AntoBrandi/Dextro-Bot/CAD/Electronics/Raspberry PI 3.SLDPRT

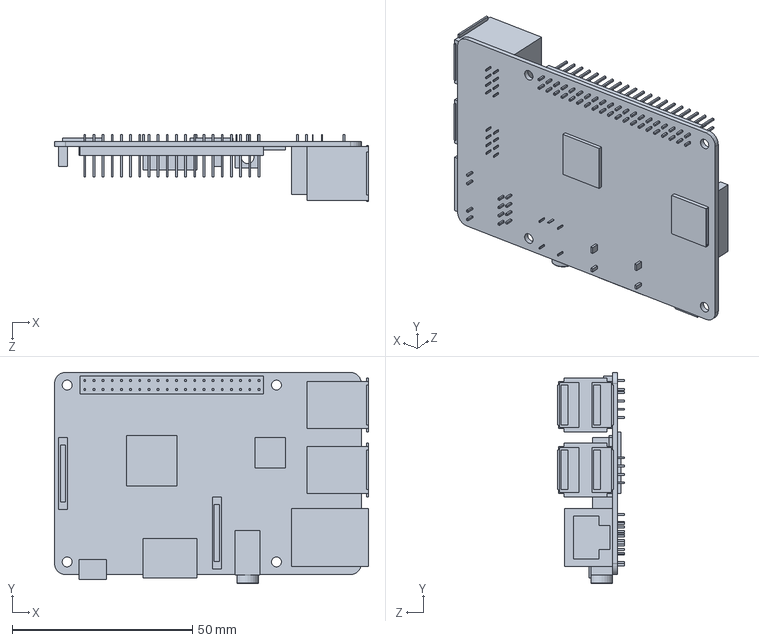
[picture p25: CAD file, 2020-10-17]
CAD/Electronics/Raspberry PI 3.SLDPRT
87.0 x 58.5 x 18.6 mm
