AntoBrandi/Dextro-Bot/CAD/pi support 1.SLDPRT

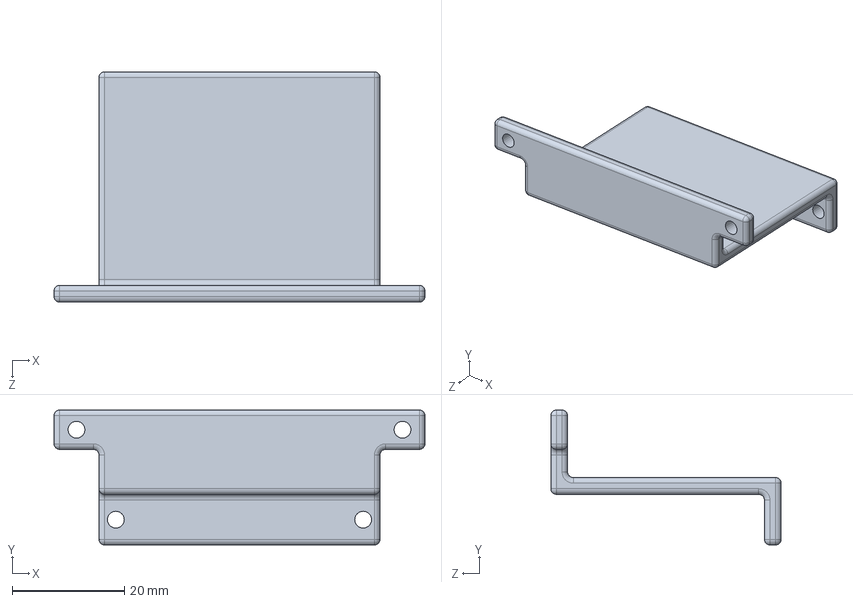
[picture p26: CAD file, 2020-08-17]
CAD/pi support 1.SLDPRT
66.0 x 24.0 x 41.0 mm
