AntoBrandi/Dextro-Bot/CAD/rev_2/carena_right.SLDPRT

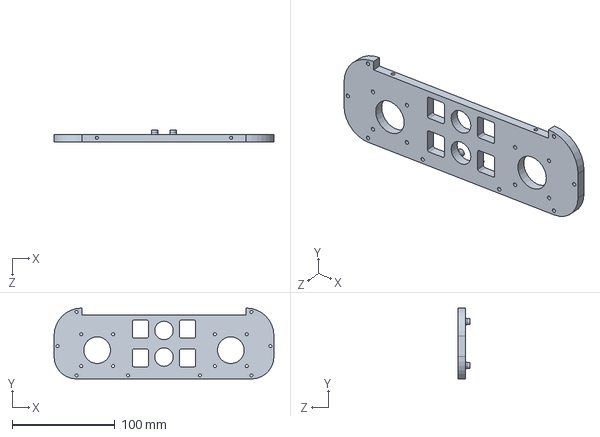
[picture p27: CAD file, 2020-10-18]
CAD/rev_2/carena_right.SLDPRT
214.0 x 69.0 x 11.5 mm
