AntoBrandi/Dextro-Bot/CAD/Servo/bottom.SLDPRT

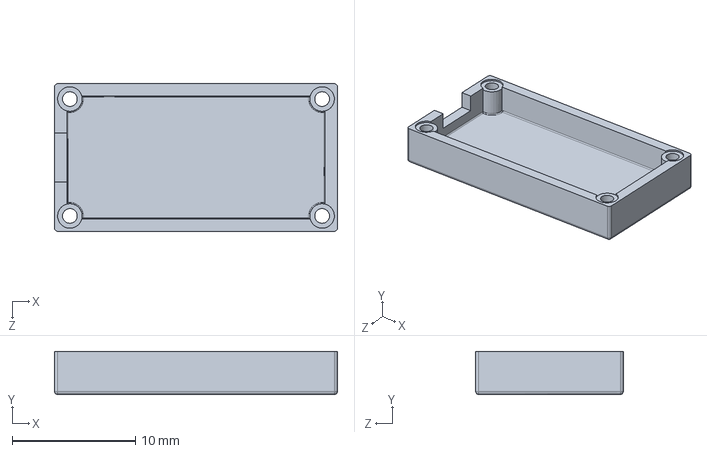
[picture p28: CAD file, 2020-07-25]
CAD/Servo/bottom.SLDPRT
23.0 x 3.50 x 12.0 mm
