AntoBrandi/Dextro-Bot/ROS/dextrobot_ws/src/robotnik_sensors/meshes/sick_microscan3.stl

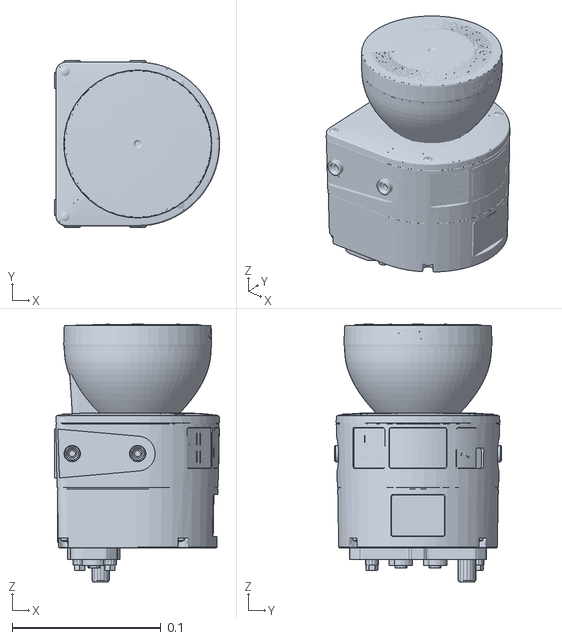
[picture p29: CAD file, 2020-08-21]
ROS/dextrobot_ws/src/robotnik_sensors/meshes/sick_microscan3.stl
0.111 x 0.112 x 0.174
