AntoBrandi/Dextro-Bot/STL/carena_top_rev.STL

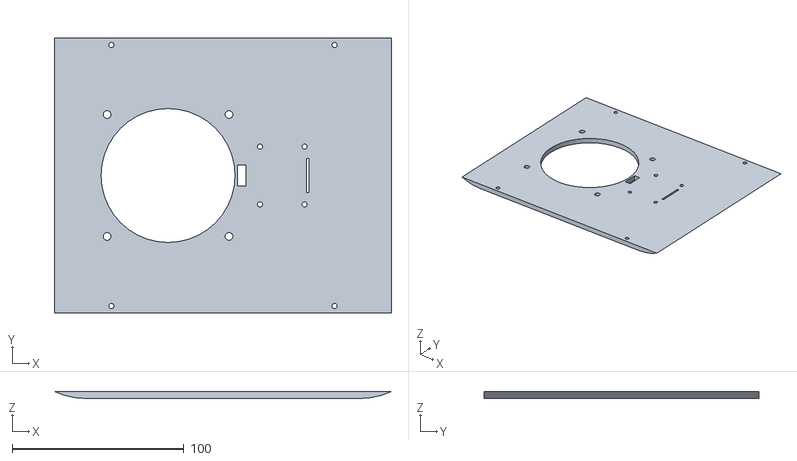
[picture p30: CAD file, 2020-07-25]
STL/carena_top_rev.STL
196.3 x 160.0 x 4.00
