AntoBrandi/Dextro-Bot/CAD/Electronics/Arduino Uno CNC Shield V3.SLDPRT

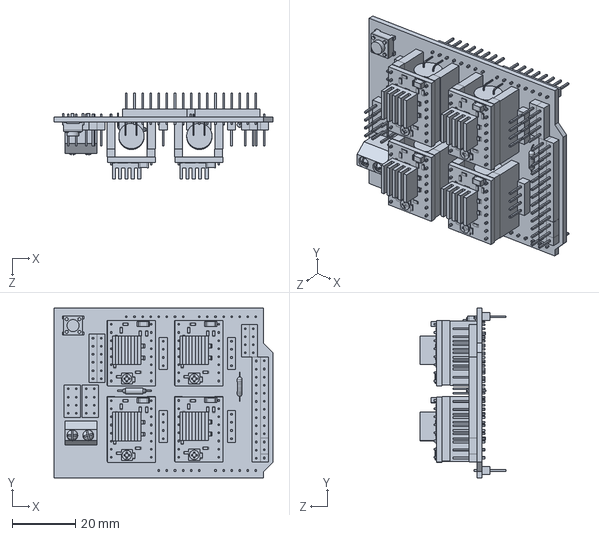
[picture p31: CAD file, 2020-10-17]
CAD/Electronics/Arduino Uno CNC Shield V3.SLDPRT
69.0 x 53.5 x 27.1 mm
