AntoBrandi/Dextro-Bot/CAD/pi support 2.SLDPRT

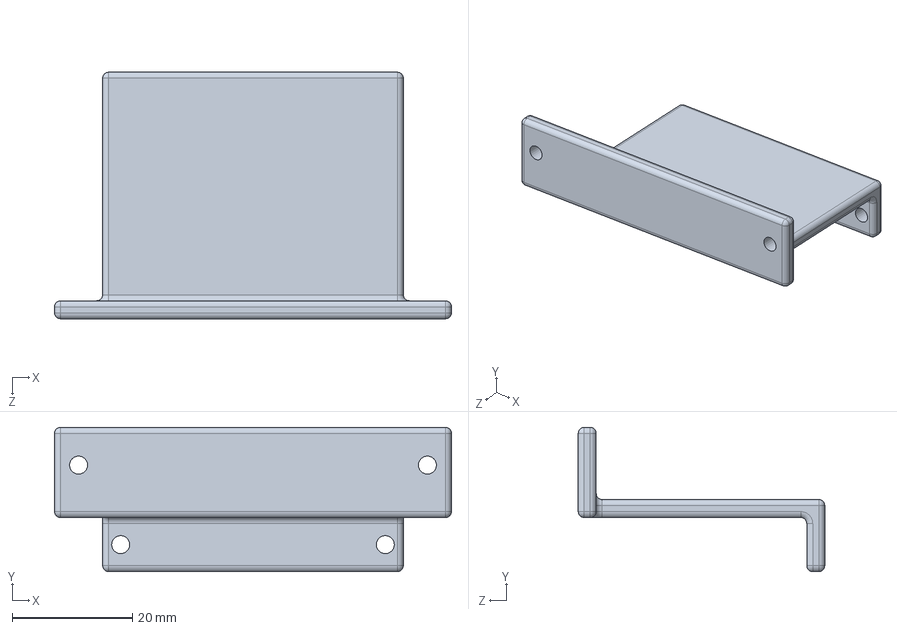
[picture p32: CAD file, 2020-08-17]
CAD/pi support 2.SLDPRT
66.0 x 24.0 x 41.0 mm
