AntoBrandi/Dextro-Bot/CAD/Servo/middle.SLDPRT

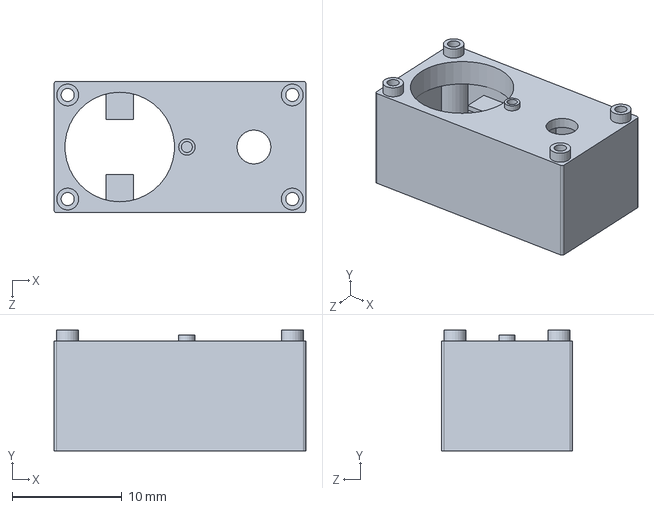
[picture p33: CAD file, 2020-07-25]
CAD/Servo/middle.SLDPRT
23.0 x 11.0 x 12.0 mm
