AntoBrandi/Dextro-Bot/ROS/dextrobot_ws/src/robotnik_sensors/meshes/antenna_3GO16.stl

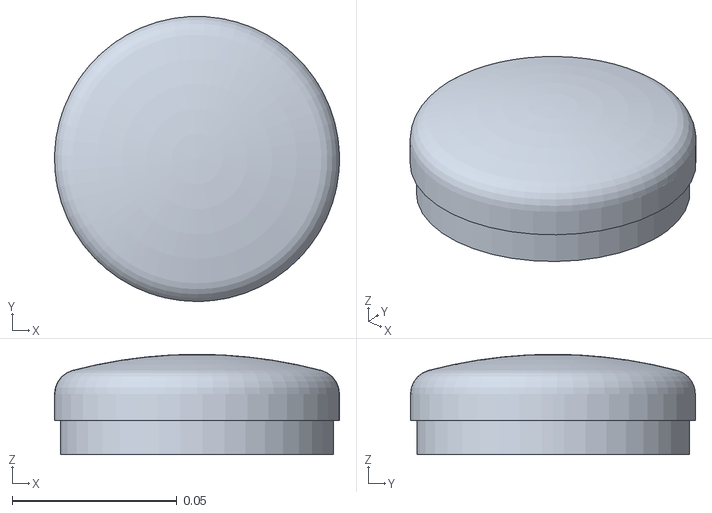
[picture p34: CAD file, 2020-08-21]
ROS/dextrobot_ws/src/robotnik_sensors/meshes/antenna_3GO16.stl
0.0866 x 0.0866 x 0.0305
