AntoBrandi/Dextro-Bot/STL/Base platform.STL

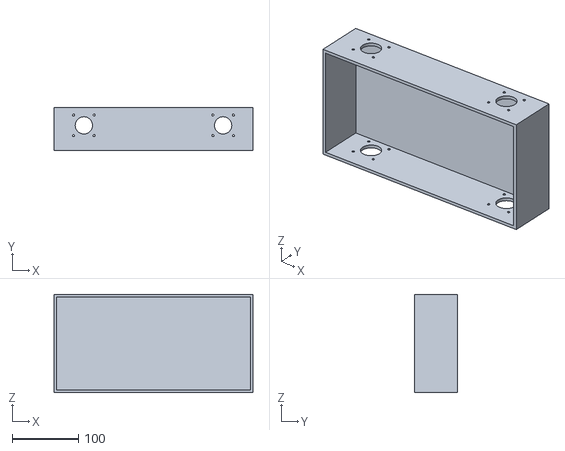
[picture p35: CAD file, 2020-07-25]
STL/Base platform.STL
300.0 x 65.0 x 148.0
