AntoBrandi/Dextro-Bot/CAD/Camera Stand v2.SLDPRT

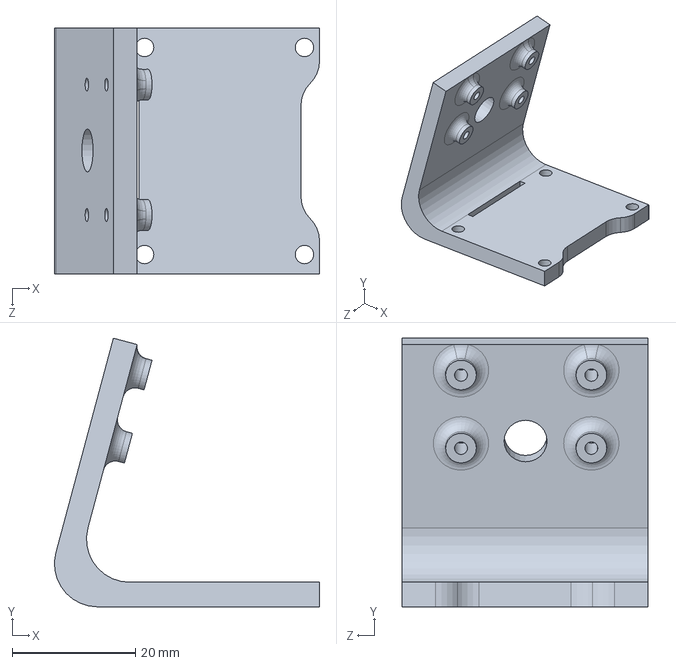
[picture p36: CAD file, 2020-08-13]
CAD/Camera Stand v2.SLDPRT
43.1 x 43.7 x 40.0 mm
