AntoBrandi/Dextro-Bot/CAD/Electronics/MPU_6050.SLDPRT

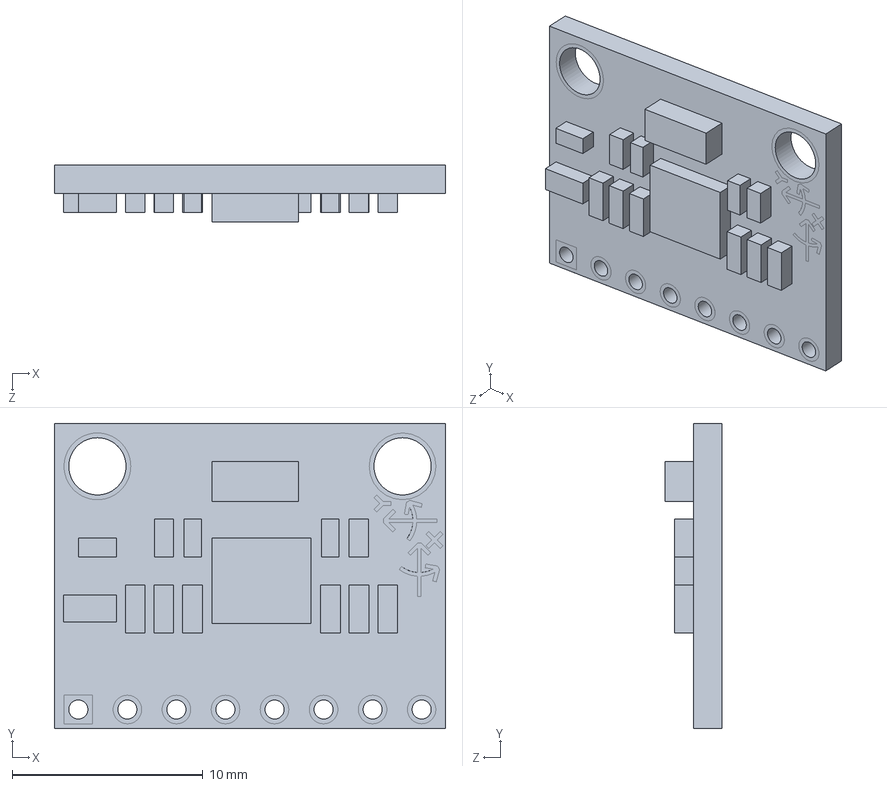
[picture p37: CAD file, 2020-10-17]
CAD/Electronics/MPU_6050.SLDPRT
20.5 x 16.0 x 3.00 mm
