AntoBrandi/Dextro-Bot/CAD/rev_2/carena_top.SLDPRT

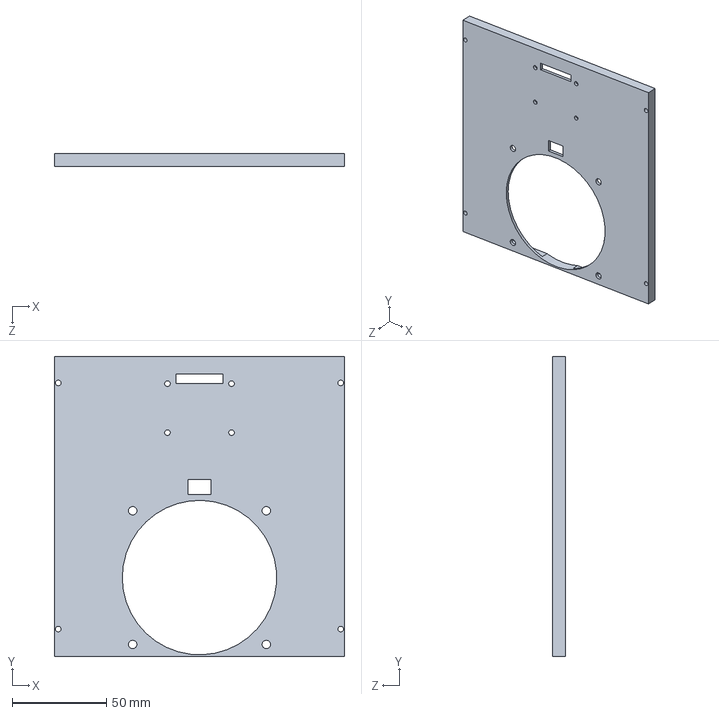
[picture p38: CAD file, 2020-10-18]
CAD/rev_2/carena_top.SLDPRT
154.0 x 159.5 x 7.00 mm
