AntoBrandi/Dextro-Bot/CAD/Servo/gear.SLDPRT

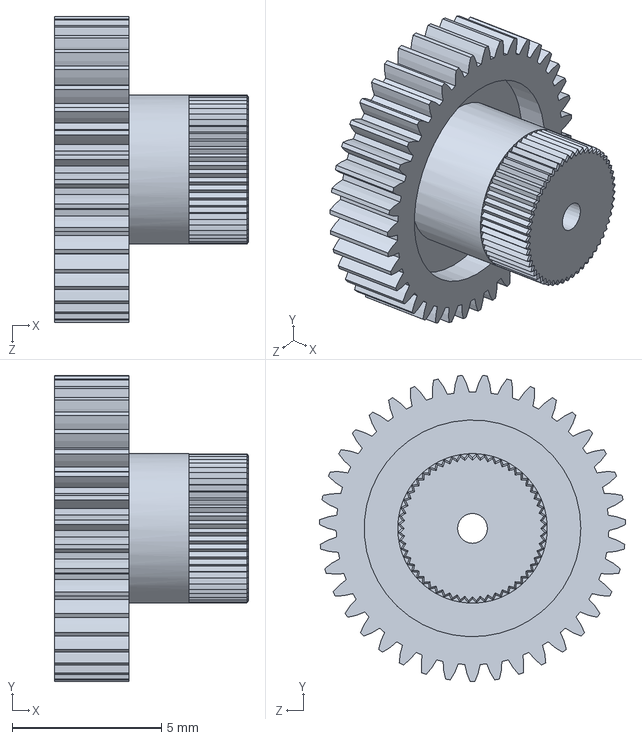
[picture p39: CAD file, 2020-07-25]
CAD/Servo/gear.SLDPRT
6.50 x 10.2 x 10.2 mm
