AntoBrandi/Dextro-Bot/ROS/dextrobot_ws/src/robotnik_sensors/meshes/hokuyo_utm_30lx.stl

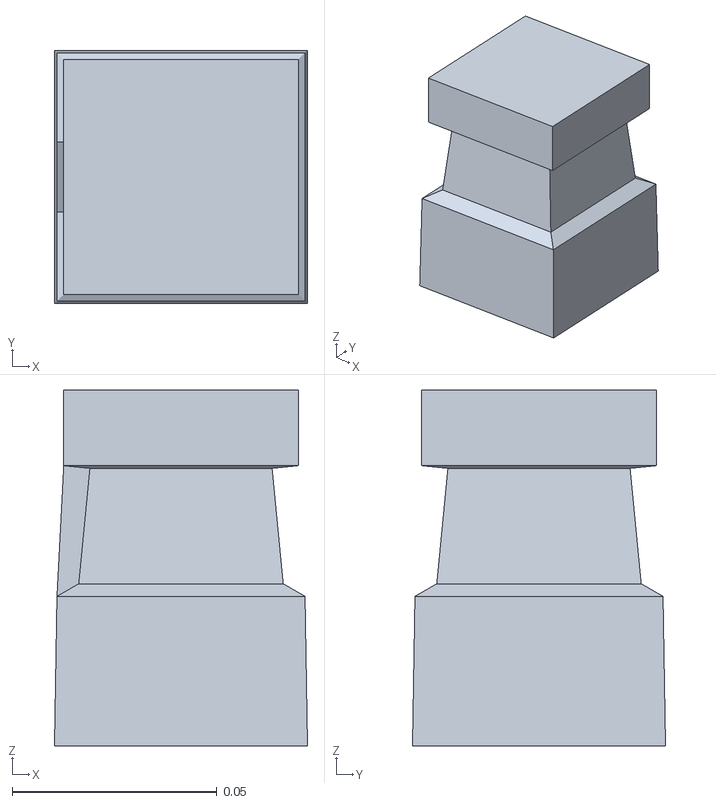
[picture p40: CAD file, 2020-08-21]
ROS/dextrobot_ws/src/robotnik_sensors/meshes/hokuyo_utm_30lx.stl
0.0618 x 0.0618 x 0.087
