AntoBrandi/Dextro-Bot/CAD/Electronics/RPi cam Rev 1.3.SLDPRT

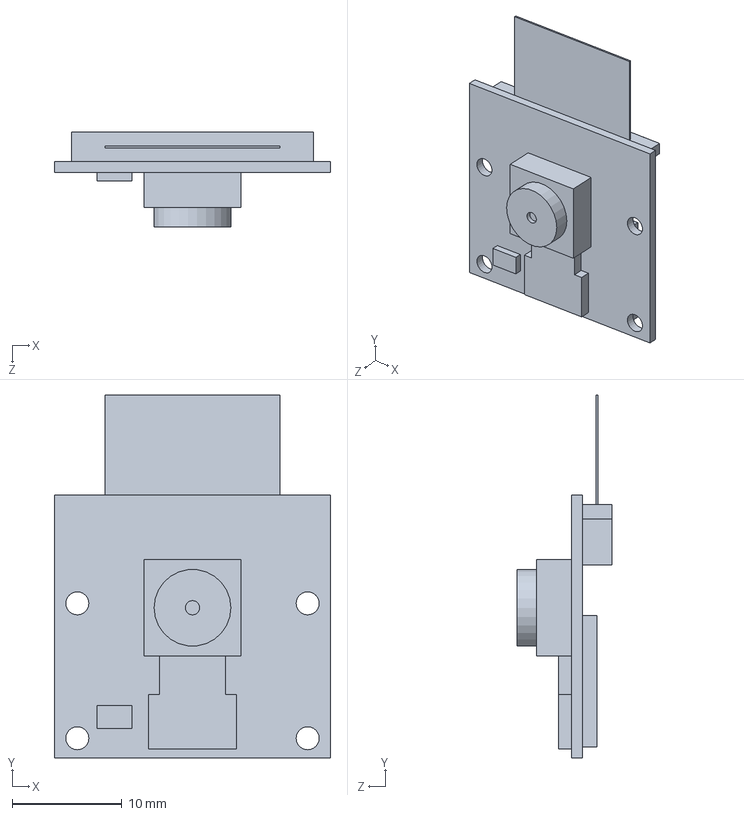
[picture p41: CAD file, 2020-07-25]
CAD/Electronics/RPi cam Rev 1.3.SLDPRT
25.2 x 33.1 x 8.70 mm
