AntoBrandi/Dextro-Bot/CAD/rev_2/battery_cover_2.SLDPRT

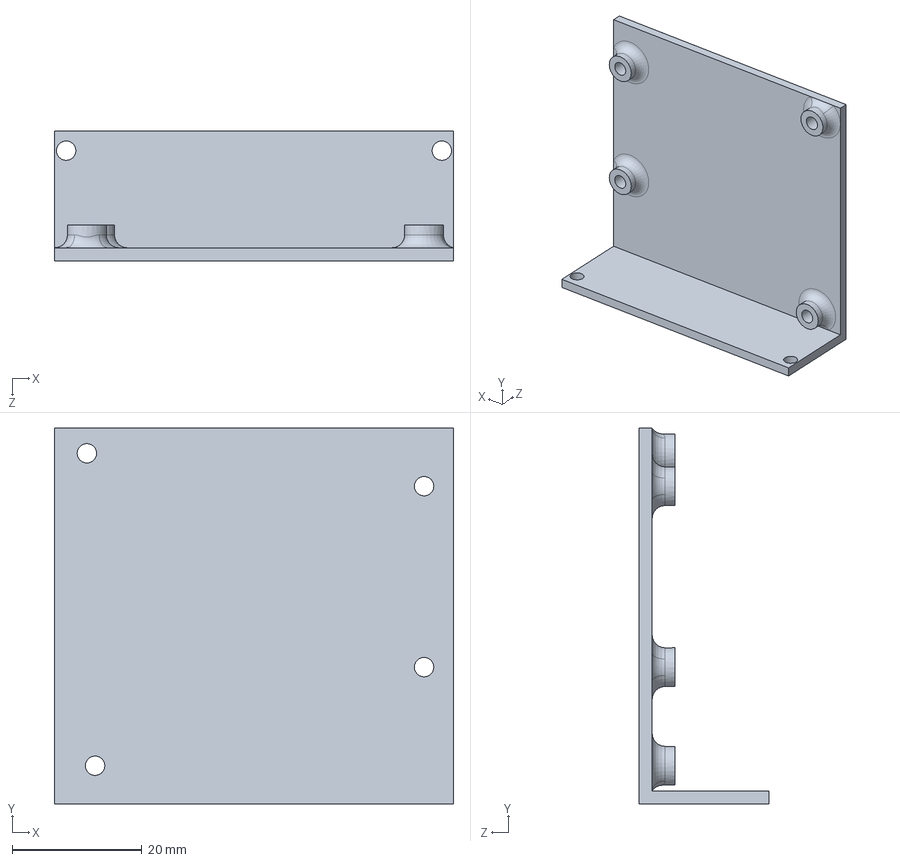
[picture p42: CAD file, 2020-10-18]
CAD/rev_2/battery_cover_2.SLDPRT
61.6 x 58.0 x 20.0 mm
