AntoBrandi/Dextro-Bot/ROS/dextrobot_ws/src/robotnik_sensors/meshes/intel_r430.stl

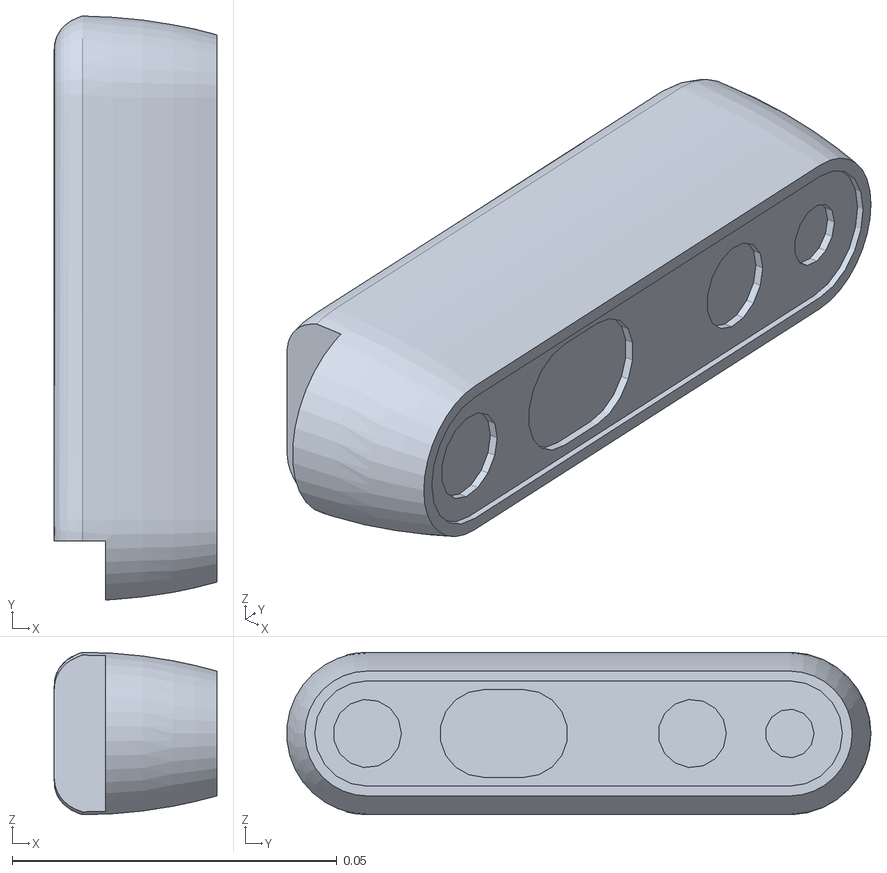
[picture p43: CAD file, 2020-08-21]
ROS/dextrobot_ws/src/robotnik_sensors/meshes/intel_r430.stl
0.025 x 0.0899 x 0.025
