AntoBrandi/Dextro-Bot/CAD/Electronics/FemaleUSB.SLDPRT

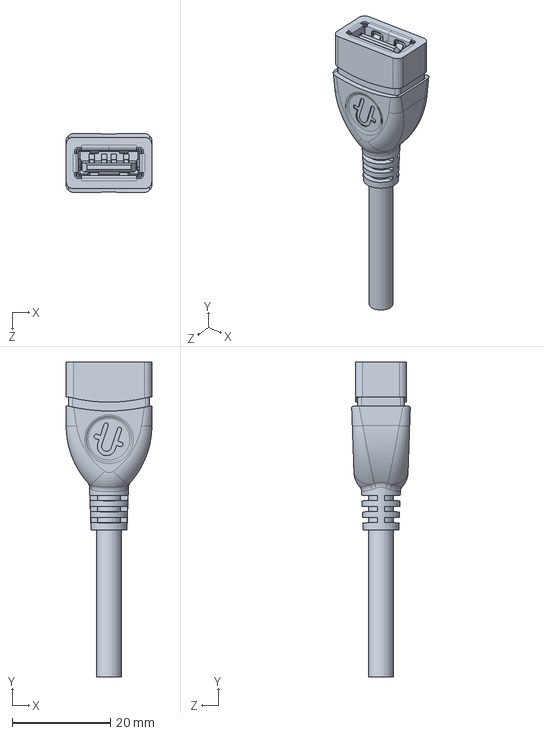
[picture p44: CAD file, 2020-07-25]
CAD/Electronics/FemaleUSB.SLDPRT
17.5 x 64.2 x 12.0 mm
