AntoBrandi/Dextro-Bot/CAD/Servo/top.SLDPRT

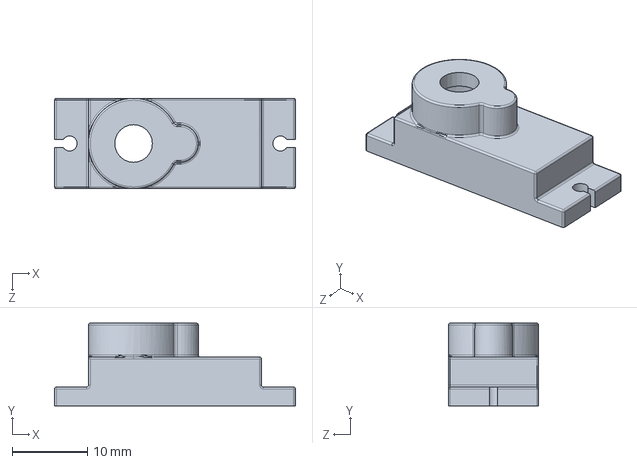
[picture p45: CAD file, 2020-07-25]
CAD/Servo/top.SLDPRT
32.0 x 11.0 x 12.0 mm
