AntoBrandi/Dextro-Bot/CAD/Electronics/XT60_Conector.SLDPRT

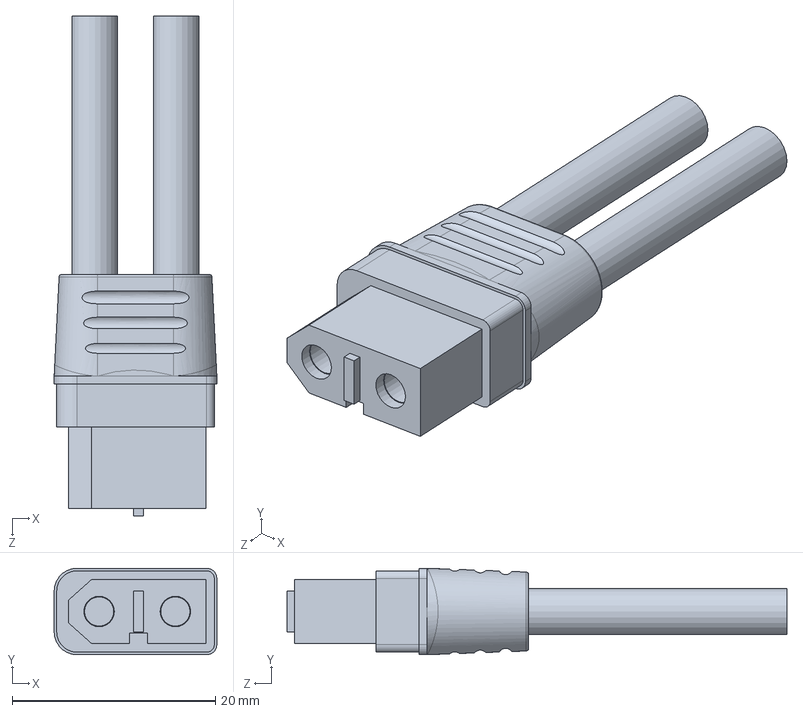
[picture p46: CAD file, 2020-07-25]
CAD/Electronics/XT60_Conector.SLDPRT
16.0 x 8.50 x 49.2 mm
