AntoBrandi/Dextro-Bot/CAD/rev_2/battery_cover_3.SLDPRT

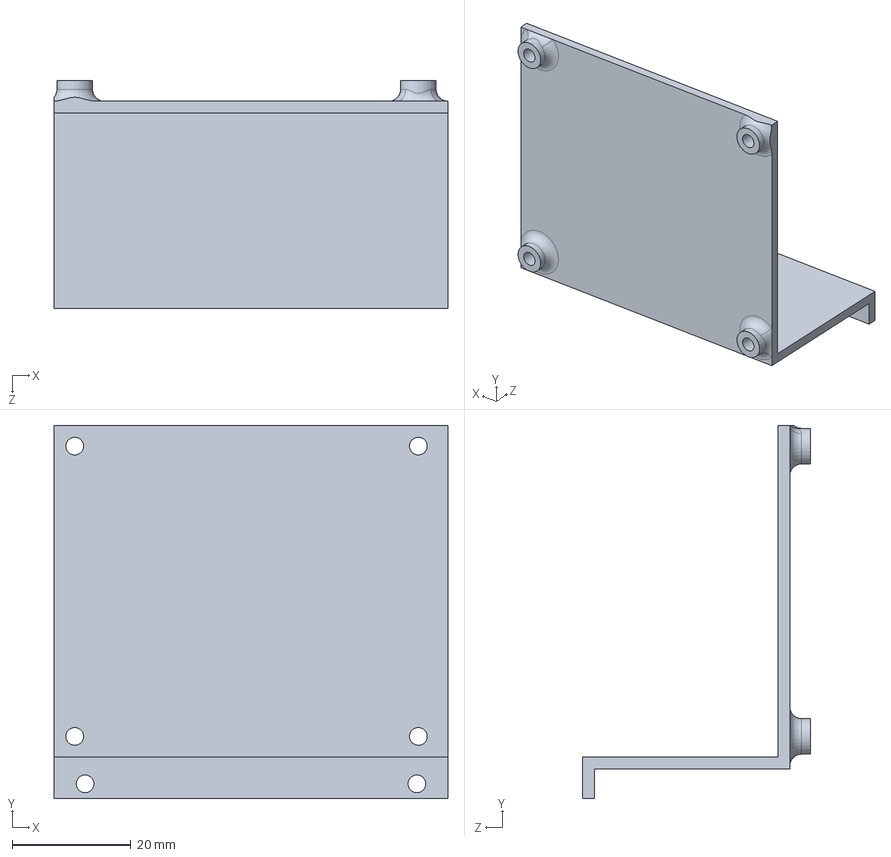
[picture p47: CAD file, 2020-10-18]
CAD/rev_2/battery_cover_3.SLDPRT
66.5 x 63.0 x 38.5 mm
