AntoBrandi/Dextro-Bot/ROS/dextrobot_ws/src/robotnik_sensors/meshes/axis_m5013.stl

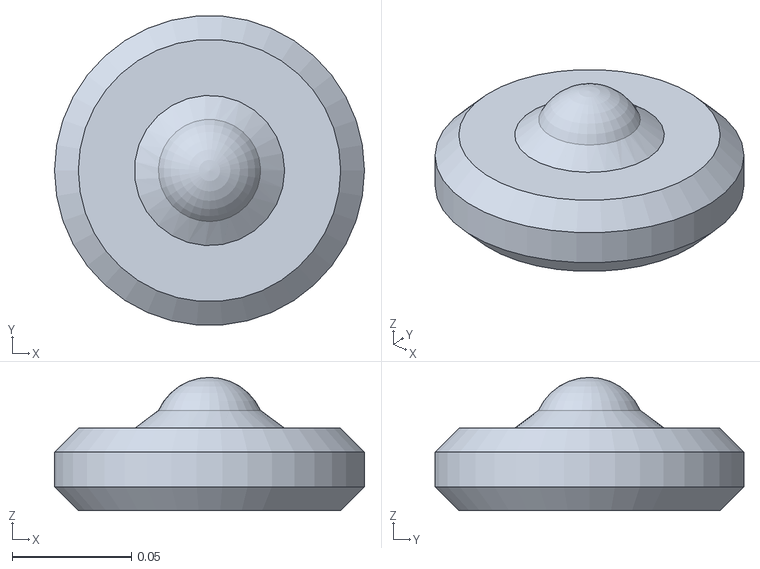
[picture p48: CAD file, 2020-08-21]
ROS/dextrobot_ws/src/robotnik_sensors/meshes/axis_m5013.stl
0.13 x 0.13 x 0.0559
