AntoBrandi/Dextro-Bot/CAD/Electronics/Nokia 6.1 plus.SLDPRT

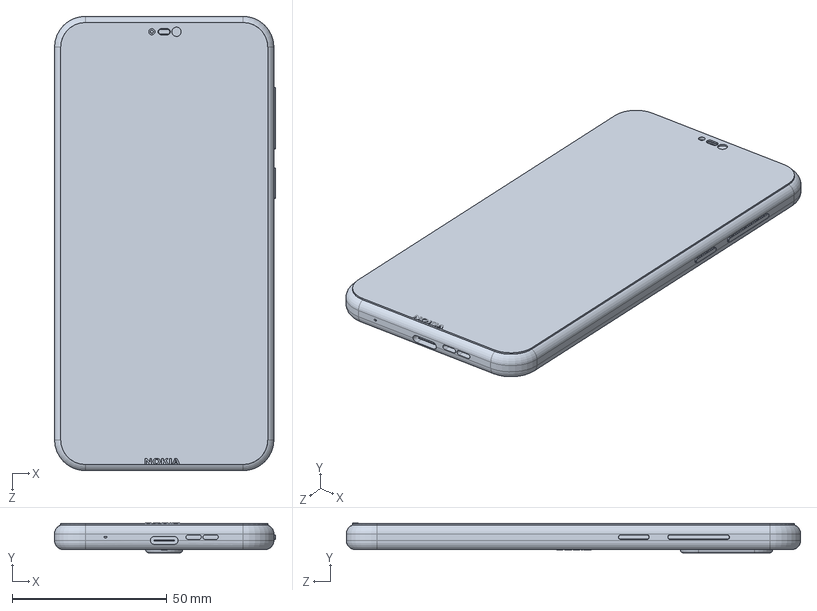
[picture p49: CAD file, 2020-07-25]
CAD/Electronics/Nokia 6.1 plus.SLDPRT
71.5 x 9.60 x 147.0 mm
