AntoBrandi/Dextro-Bot/CAD/rev_2/battery_cover.SLDPRT

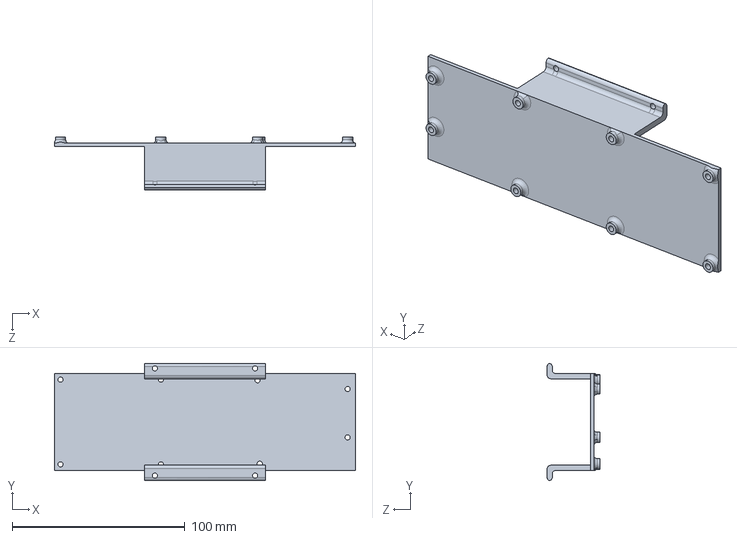
[picture p50: CAD file, 2020-10-17]
CAD/rev_2/battery_cover.SLDPRT
174.0 x 67.9 x 30.5 mm
