AntoBrandi/Dextro-Bot/ROS/dextrobot_ws/src/robotnik_sensors/meshes/ueye_cp_gige.stl

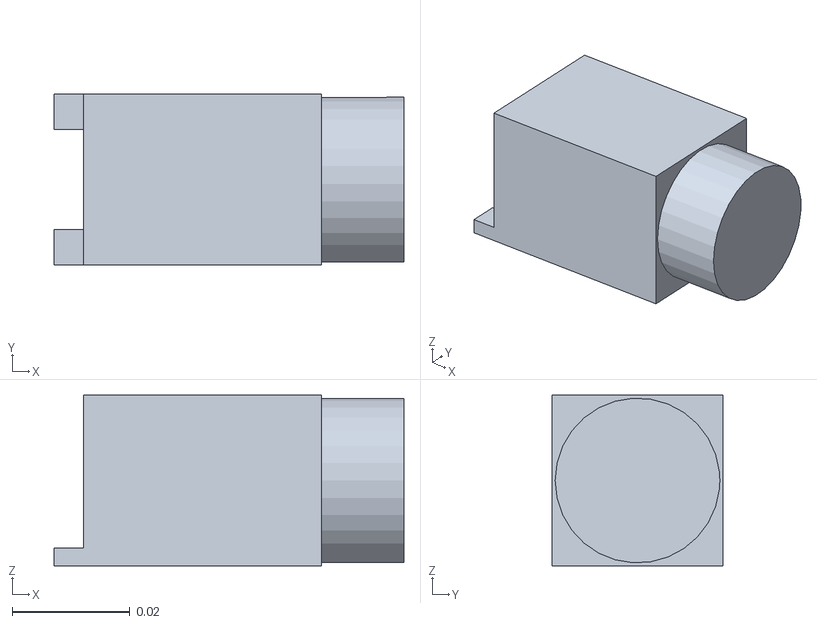
[picture p51: CAD file, 2020-08-21]
ROS/dextrobot_ws/src/robotnik_sensors/meshes/ueye_cp_gige.stl
0.0595 x 0.029 x 0.029
