AntoBrandi/Dextro-Bot/CAD/Electronics/Nema17.SLDPRT

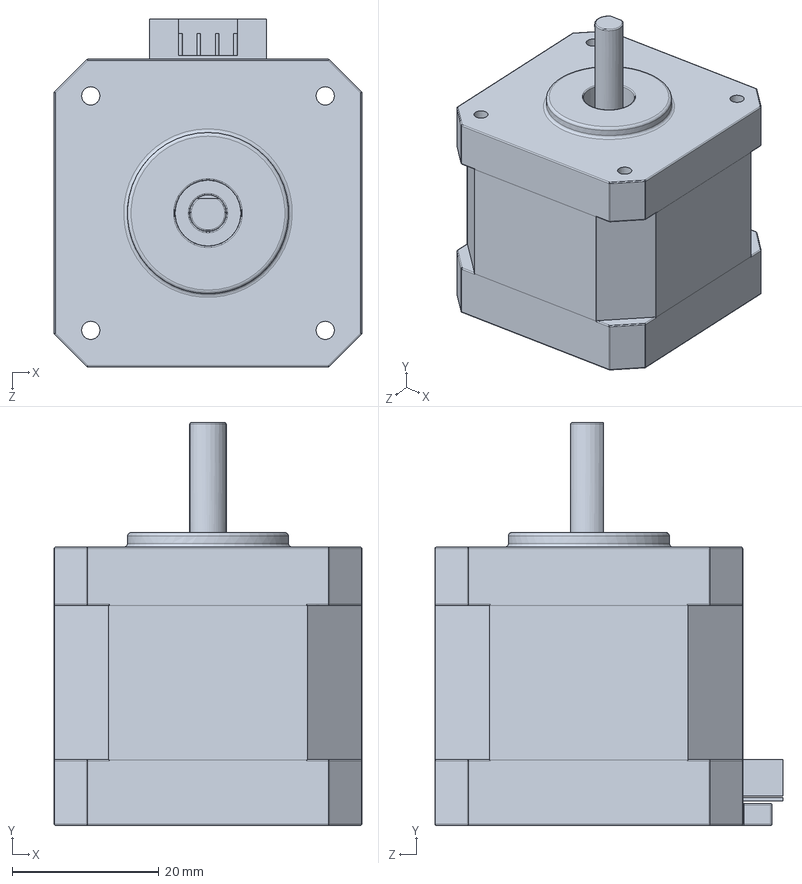
[picture p52: CAD file, 2020-07-25]
CAD/Electronics/Nema17.SLDPRT
42.0 x 55.0 x 47.5 mm
