AntoBrandi/Dextro-Bot/ROS/dextrobot_ws/src/robotnik_sensors/meshes/benewake_ce30.stl

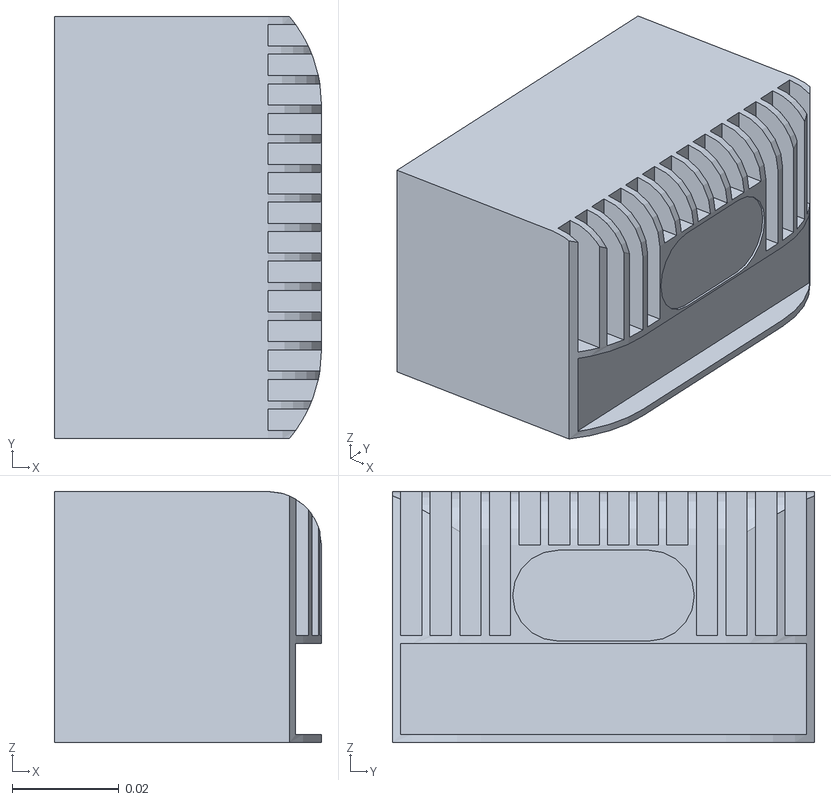
[picture p53: CAD file, 2020-08-21]
ROS/dextrobot_ws/src/robotnik_sensors/meshes/benewake_ce30.stl
0.05 x 0.079 x 0.047
