AntoBrandi/Dextro-Bot/CAD/Electronics/DRV 8825 .SLDPRT

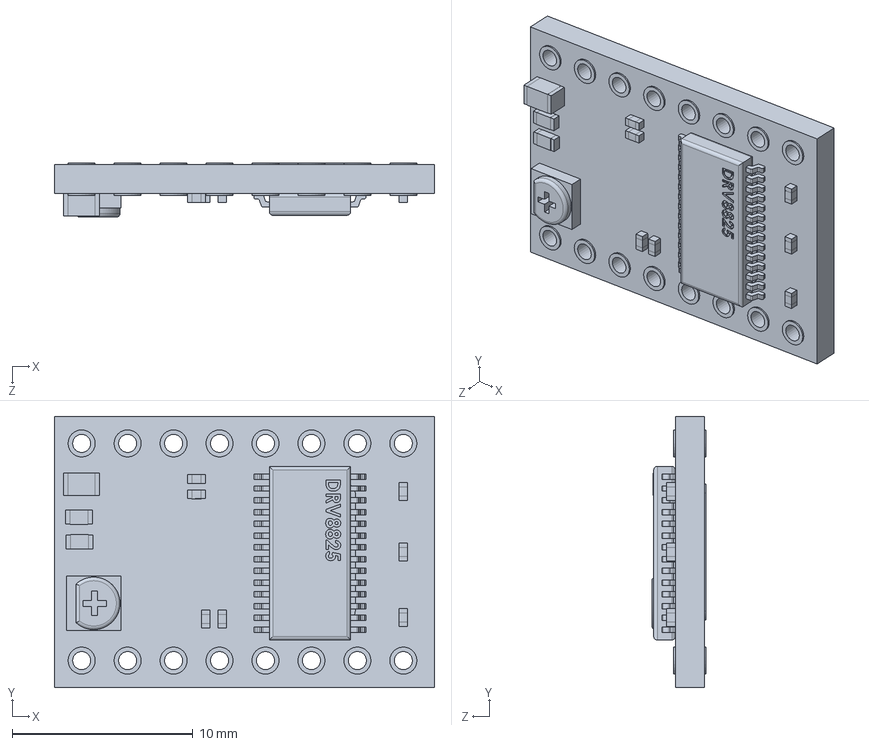
[picture p54: CAD file, 2020-07-25]
CAD/Electronics/DRV 8825 .SLDPRT
21.0 x 15.0 x 3.00 mm
