AntoBrandi/Dextro-Bot/ROS/dextrobot_ws/src/robotnik_sensors/meshes/kinectv2_nobase.stl

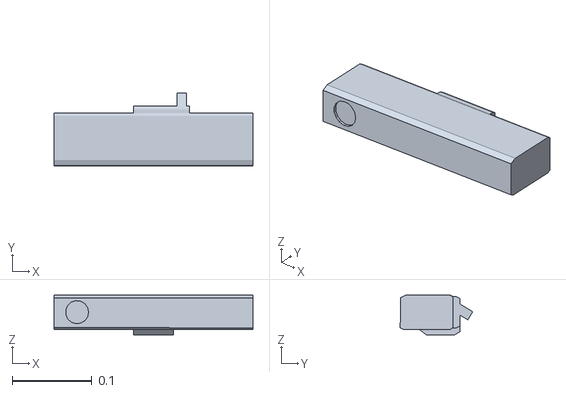
[picture p55: CAD file, 2020-08-21]
ROS/dextrobot_ws/src/robotnik_sensors/meshes/kinectv2_nobase.stl
0.25 x 0.0911 x 0.0501
