AntoBrandi/Dextro-Bot/CAD/Electronics/Female HDMI connector.SLDPRT

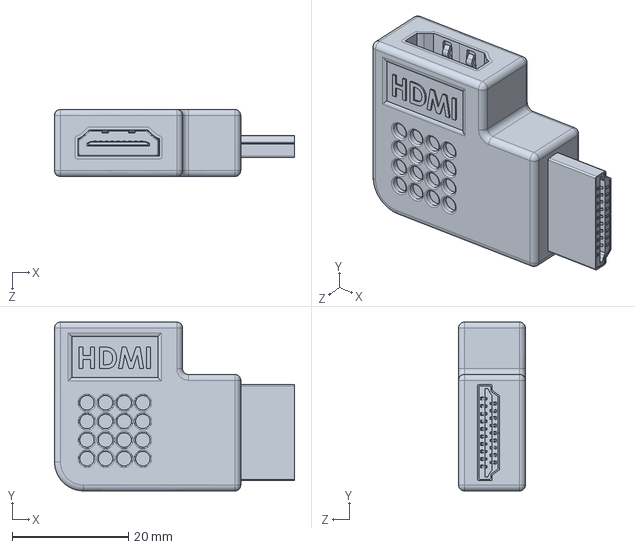
[picture p56: CAD file, 2020-07-25]
CAD/Electronics/Female HDMI connector.SLDPRT
41.2 x 29.0 x 11.5 mm
