AntoBrandi/Dextro-Bot/ROS/dextrobot_ws/src/robotnik_sensors/meshes/rslidar.stl

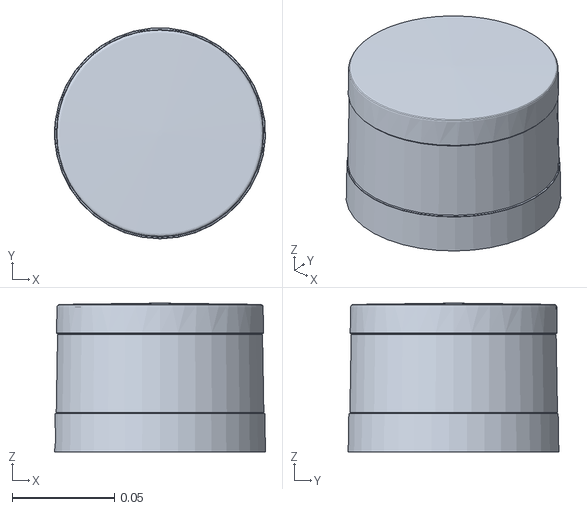
[picture p57: CAD file, 2020-08-21]
ROS/dextrobot_ws/src/robotnik_sensors/meshes/rslidar.stl
0.103 x 0.103 x 0.0727
