AntoBrandi/Dextro-Bot/CAD/Electronics/5 cell LiPo battery v7.SLDPRT

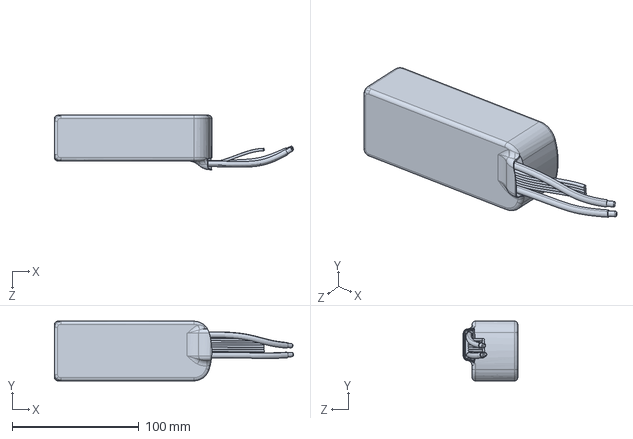
[picture p58: CAD file, 2020-07-25]
CAD/Electronics/5 cell LiPo battery v7.SLDPRT
188.3 x 47.0 x 43.0 mm
