AntoBrandi/Dextro-Bot/ROS/dextrobot_ws/src/robotnik_sensors/meshes/zed.stl

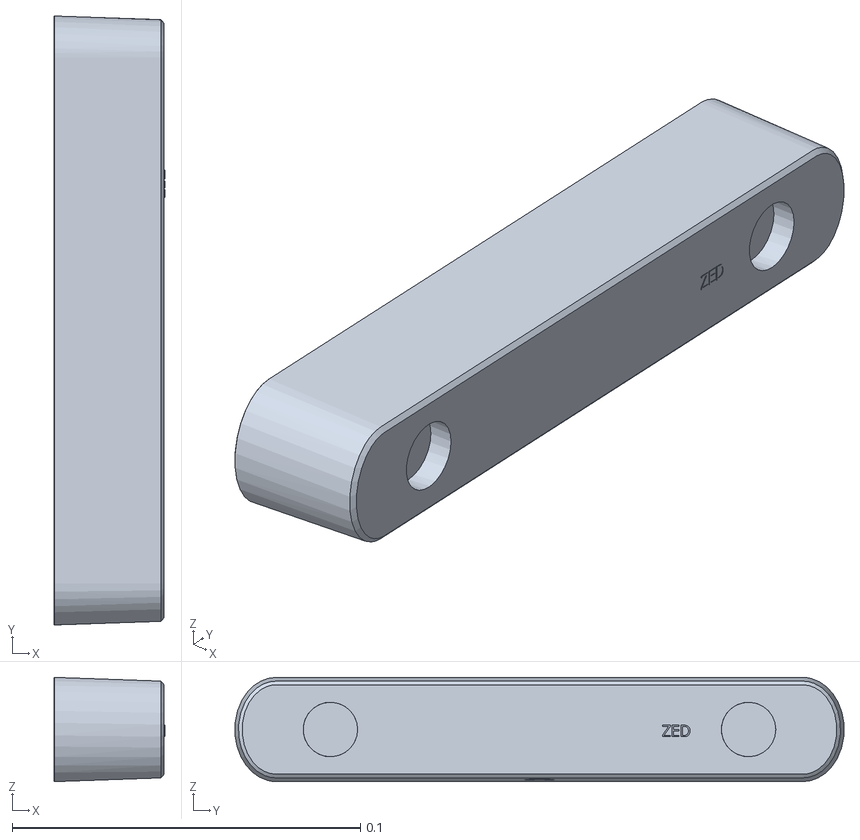
[picture p59: CAD file, 2020-08-21]
ROS/dextrobot_ws/src/robotnik_sensors/meshes/zed.stl
0.0318 x 0.175 x 0.0299
