AntoBrandi/Dextro-Bot/CAD/Roller.SLDPRT

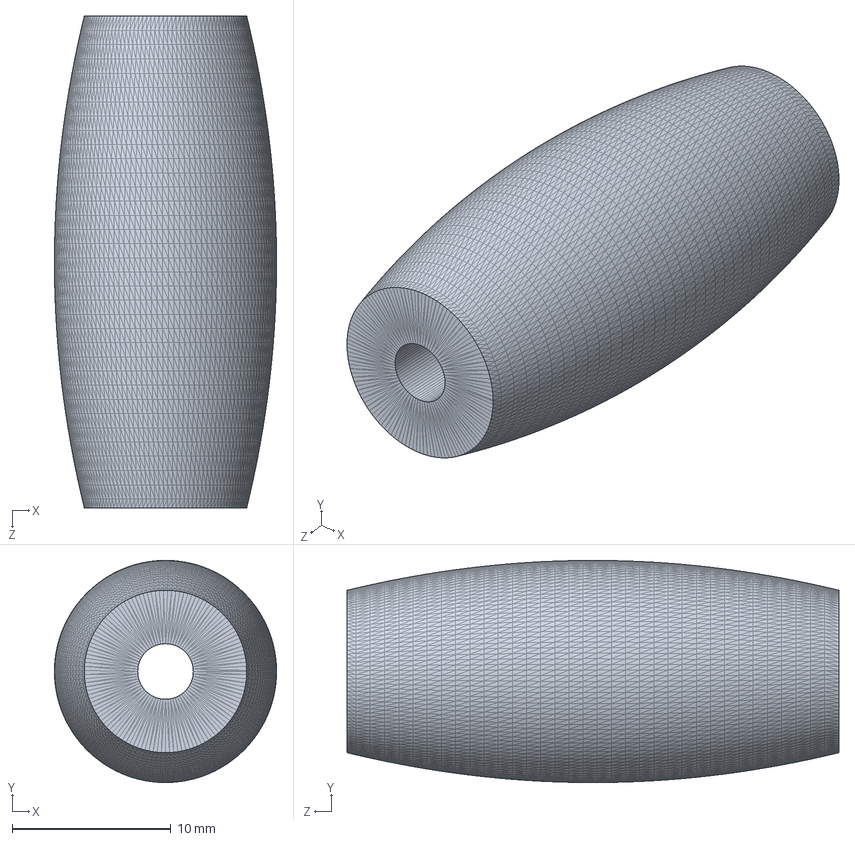
[picture p60: CAD file, 2020-07-25]
CAD/Roller.SLDPRT
14.0 x 14.0 x 31.0 mm
