AntoBrandi/Dextro-Bot/ROS/dextrobot_ws/src/robotnik_sensors/meshes/fotonic_e.stl

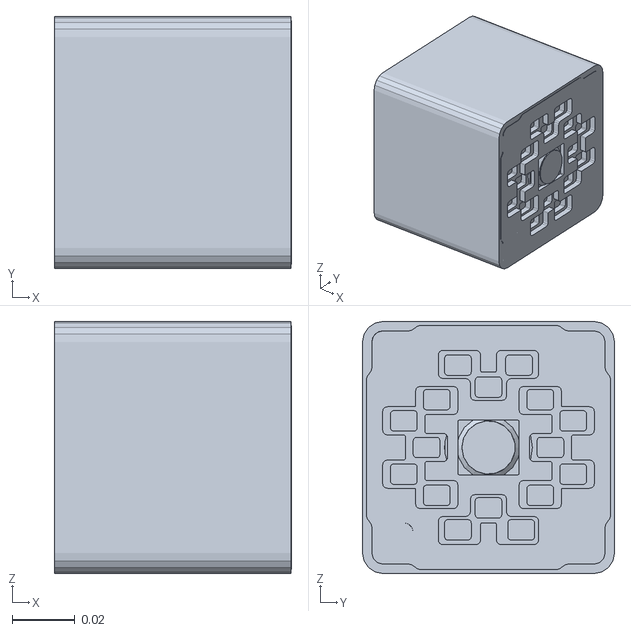
[picture p61: CAD file, 2020-08-21]
ROS/dextrobot_ws/src/robotnik_sensors/meshes/fotonic_e.stl
0.0756 x 0.0803 x 0.0804
