AntoBrandi/Dextro-Bot/ROS/dextrobot_ws/src/robotnik_sensors/meshes/sick_s300.stl

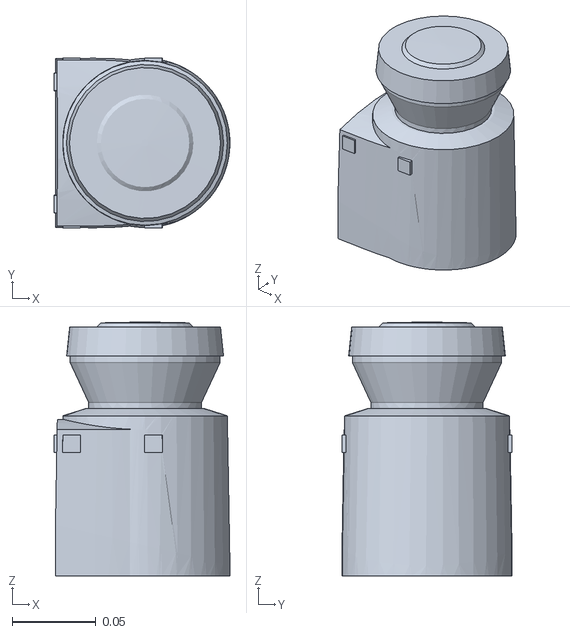
[picture p62: CAD file, 2020-08-21]
ROS/dextrobot_ws/src/robotnik_sensors/meshes/sick_s300.stl
0.105 x 0.102 x 0.152
