AntoBrandi/Dextro-Bot/ROS/dextrobot_ws/src/robotnik_sensors/meshes/teraranger_tr_duo.stl

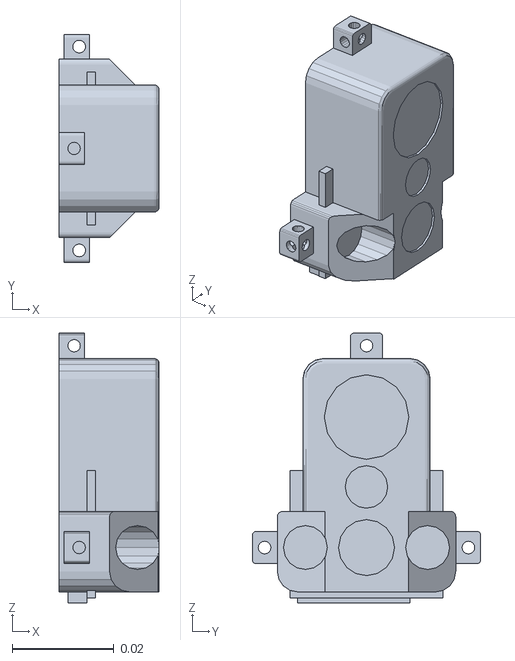
[picture p63: CAD file, 2020-08-21]
ROS/dextrobot_ws/src/robotnik_sensors/meshes/teraranger_tr_duo.stl
0.0197 x 0.0448 x 0.053
