AntoBrandi/Dextro-Bot/ROS/dextrobot_ws/src/robotnik_sensors/meshes/hokuyo3d.stl

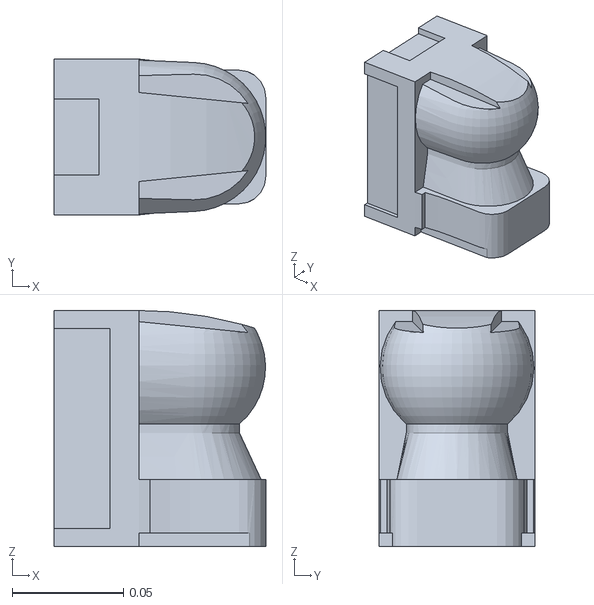
[picture p64: CAD file, 2020-08-21]
ROS/dextrobot_ws/src/robotnik_sensors/meshes/hokuyo3d.stl
0.095 x 0.07 x 0.106
