AntoBrandi/Dextro-Bot/ROS/dextrobot_ws/src/robotnik_sensors/meshes/axis_m5525.stl

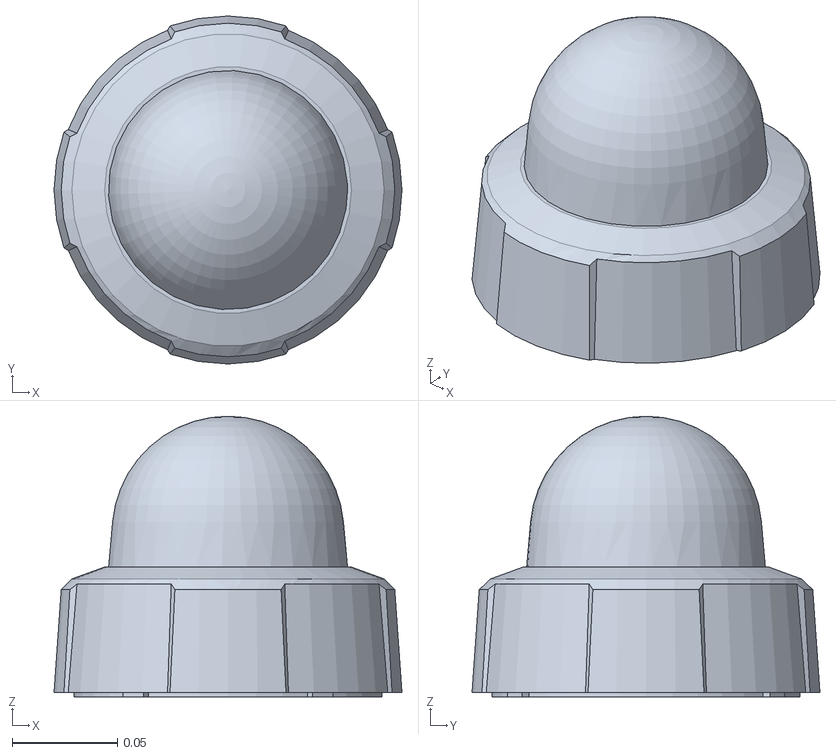
[picture p65: CAD file, 2020-08-21]
ROS/dextrobot_ws/src/robotnik_sensors/meshes/axis_m5525.stl
0.165 x 0.165 x 0.133
