AntoBrandi/Dextro-Bot/ROS/dextrobot_ws/src/robotnik_sensors/meshes/sick_tim551.stl

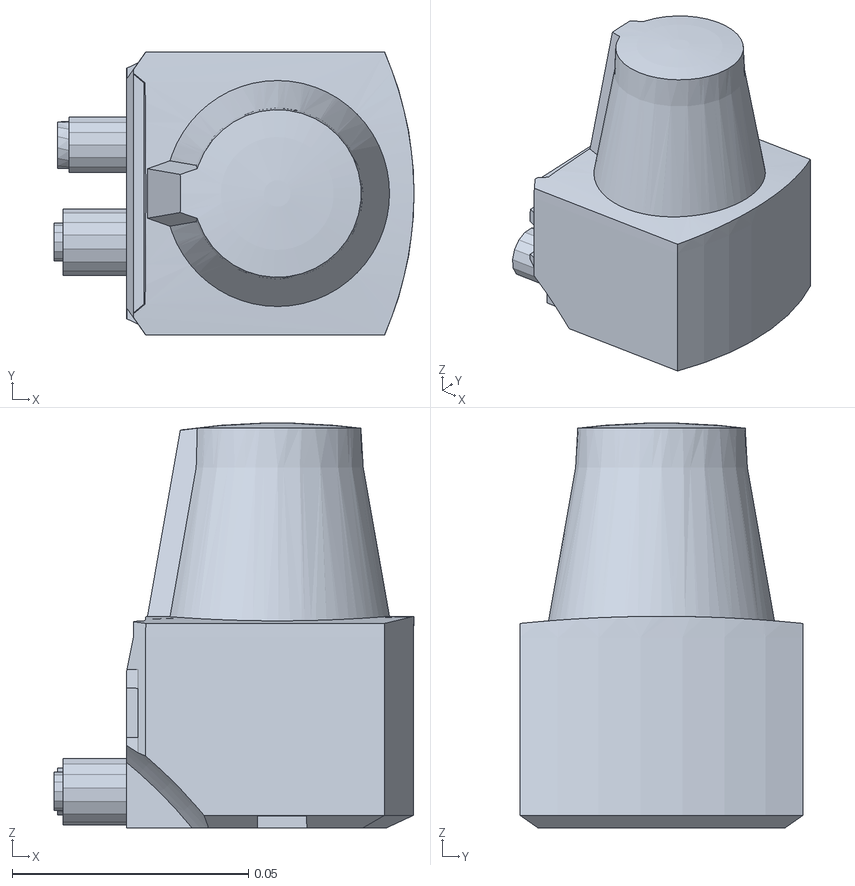
[picture p66: CAD file, 2020-08-21]
ROS/dextrobot_ws/src/robotnik_sensors/meshes/sick_tim551.stl
0.0762 x 0.06 x 0.0858
