AntoBrandi/Dextro-Bot/ROS/dextrobot_ws/src/robotnik_sensors/meshes/sick_s3000.stl

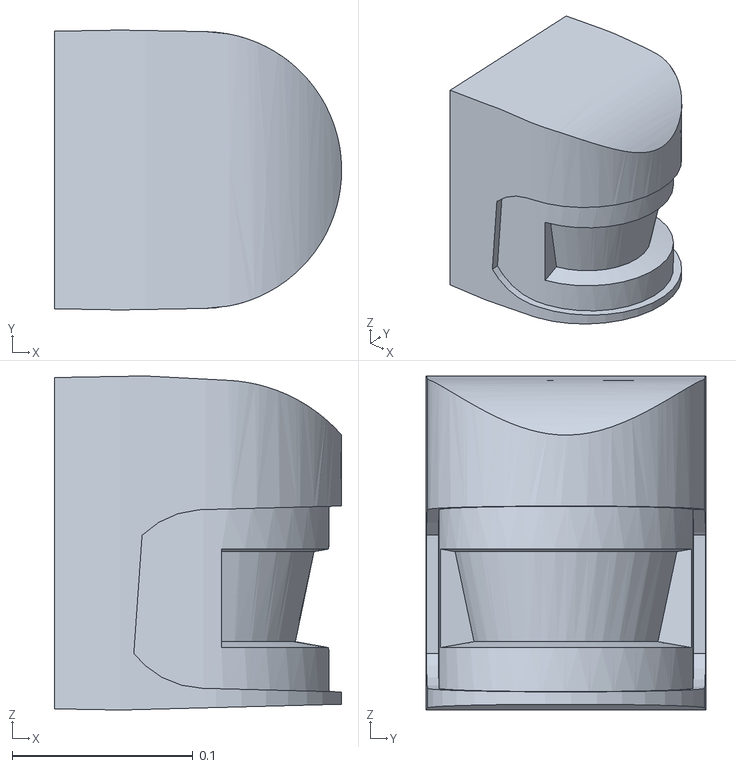
[picture p67: CAD file, 2020-08-21]
ROS/dextrobot_ws/src/robotnik_sensors/meshes/sick_s3000.stl
0.159 x 0.155 x 0.185
