AntoBrandi/Dextro-Bot/CAD/roundCover.SLDPRT

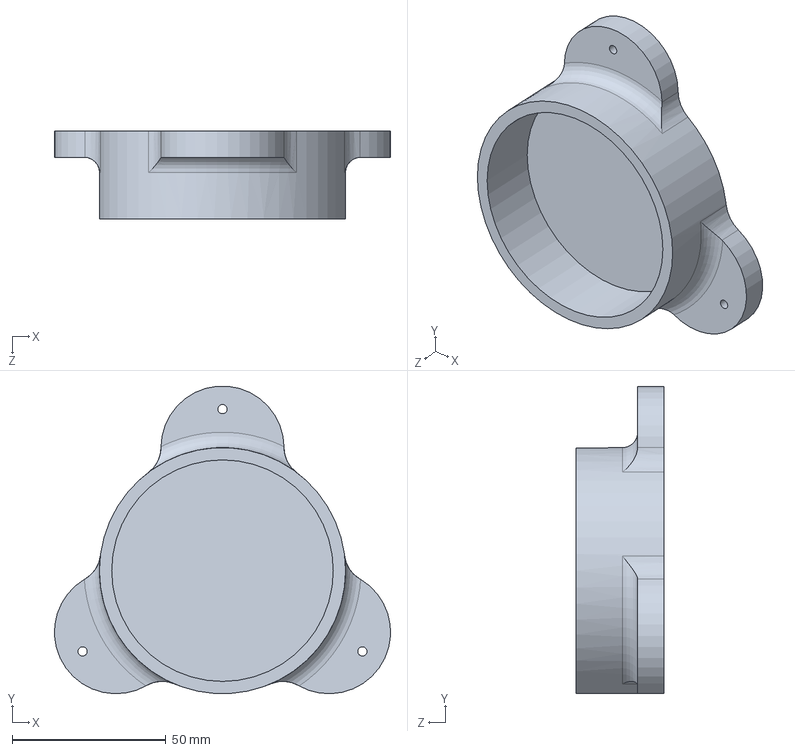
[picture p68: CAD file, 2020-07-25]
CAD/roundCover.SLDPRT
109.2 x 99.9 x 28.5 mm
