AntoBrandi/Dextro-Bot/ROS/dextrobot_ws/src/robotnik_sensors/meshes/kinectv2.stl

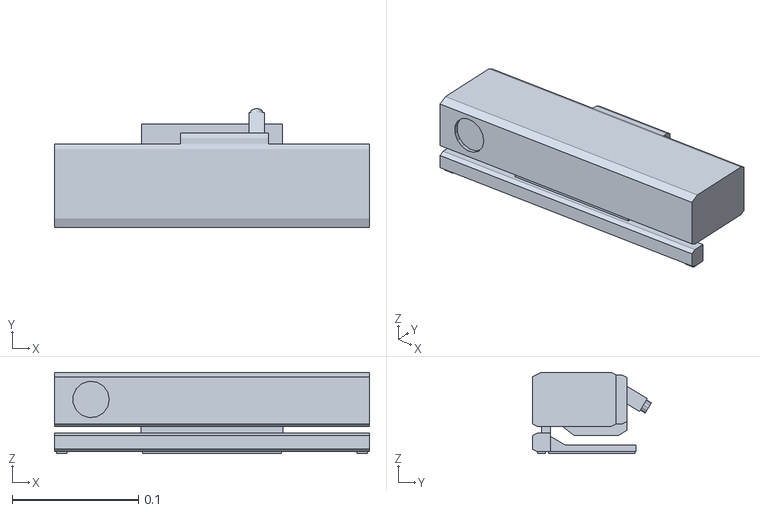
[picture p69: CAD file, 2020-08-21]
ROS/dextrobot_ws/src/robotnik_sensors/meshes/kinectv2.stl
0.25 x 0.0943 x 0.0645
