AntoBrandi/Dextro-Bot/ROS/dextrobot_ws/src/robotnik_sensors/meshes/hokuyo_urg_04lx.stl

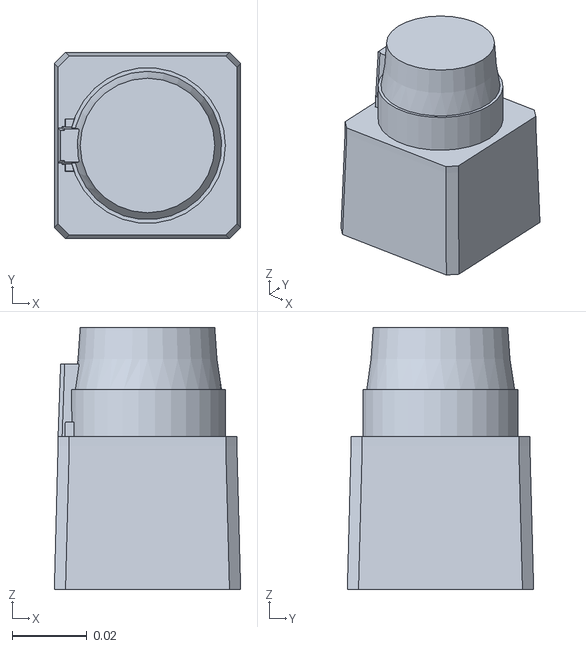
[picture p70: CAD file, 2020-08-21]
ROS/dextrobot_ws/src/robotnik_sensors/meshes/hokuyo_urg_04lx.stl
0.05 x 0.05 x 0.0703
