AntoBrandi/Dextro-Bot/CAD/Right carena.SLDPRT

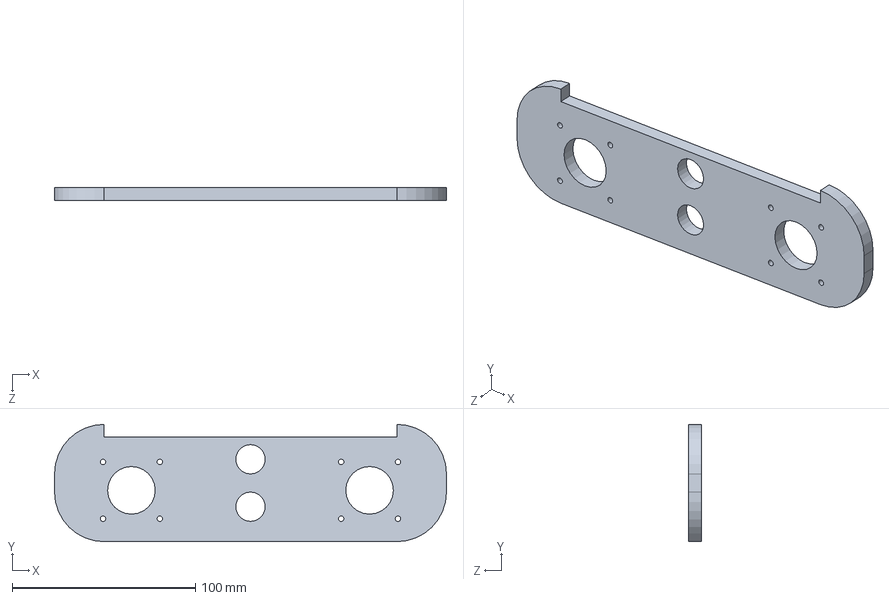
[picture p71: CAD file, 2020-07-25]
CAD/Right carena.SLDPRT
214.0 x 64.0 x 7.00 mm
