AntoBrandi/Dextro-Bot/ROS/dextrobot_ws/src/robotnik_sensors/meshes/orbbec_astra.stl

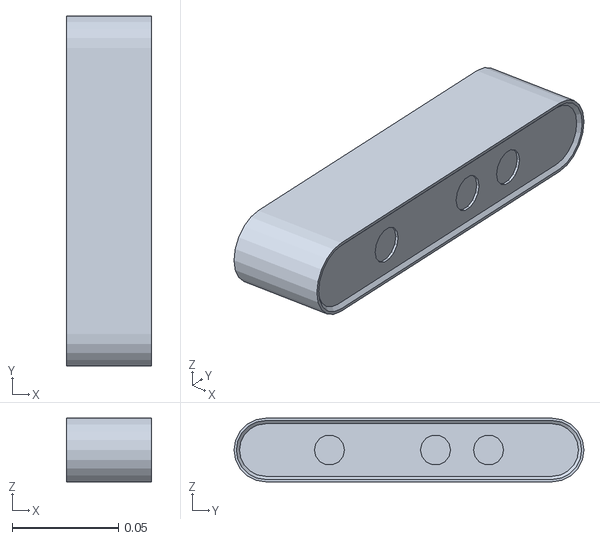
[picture p72: CAD file, 2020-08-21]
ROS/dextrobot_ws/src/robotnik_sensors/meshes/orbbec_astra.stl
0.04 x 0.165 x 0.03
