AntoBrandi/Dextro-Bot/CAD/Wheel base plate Left.SLDPRT

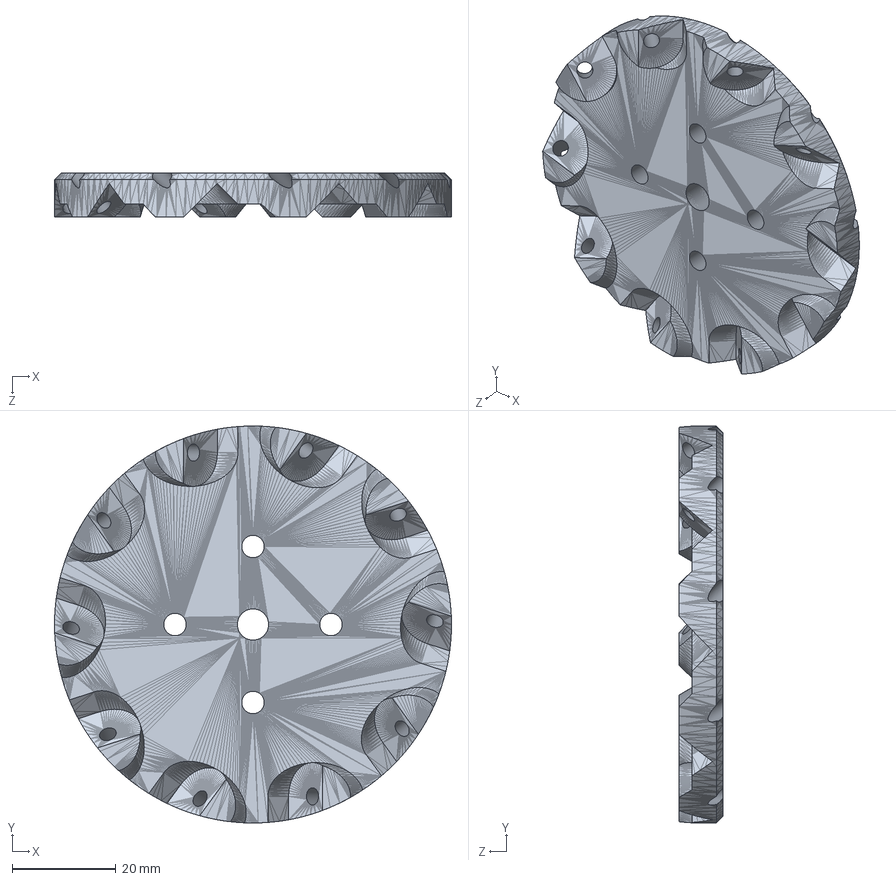
[picture p73: CAD file, 2020-07-25]
CAD/Wheel base plate Left.SLDPRT
76.4 x 76.4 x 8.50 mm
