AntoBrandi/Dextro-Bot/CAD/roundBase.SLDPRT

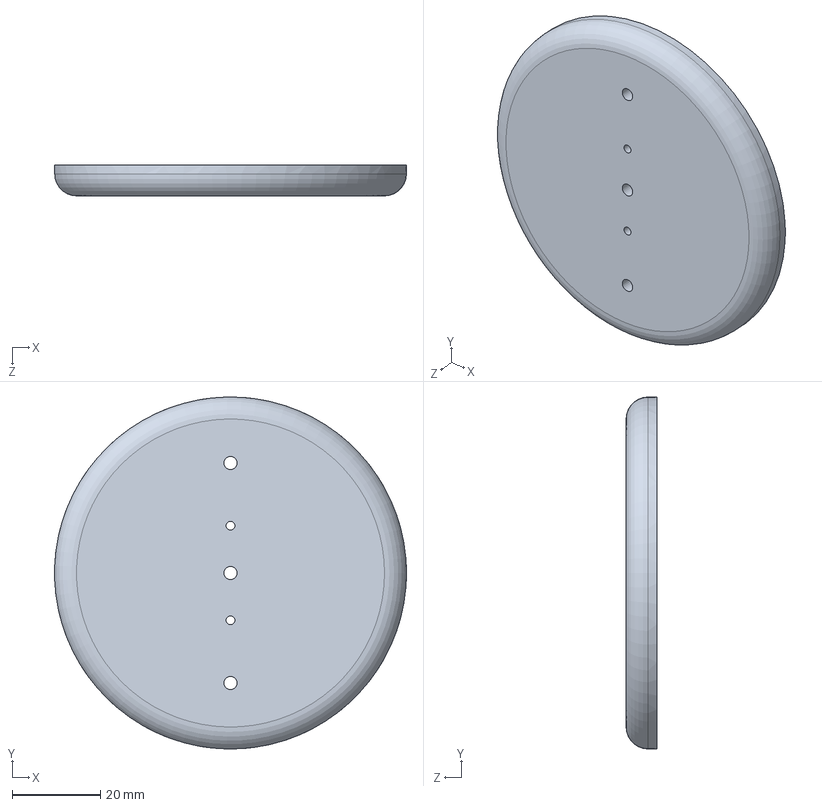
[picture p74: CAD file, 2020-07-25]
CAD/roundBase.SLDPRT
80.0 x 80.0 x 7.00 mm
