AntoBrandi/Dextro-Bot/CAD/carena_top_2.SLDPRT

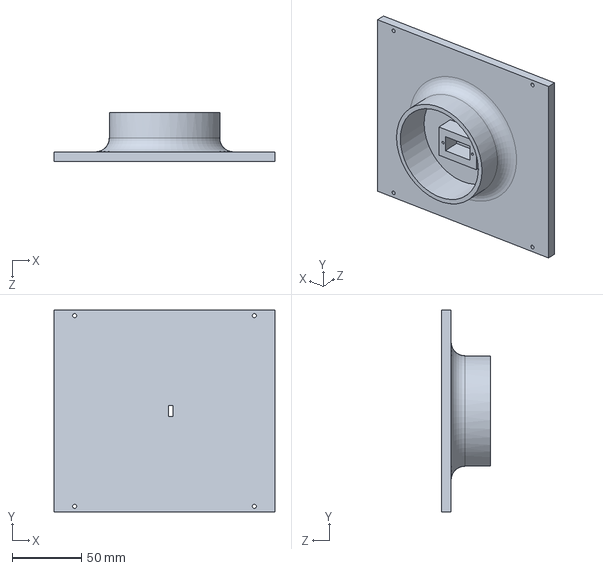
[picture p75: CAD file, 2020-07-25]
CAD/carena_top_2.SLDPRT
160.0 x 146.0 x 35.5 mm
