AntoBrandi/Dextro-Bot/ROS/dextrobot_ws/src/dextrobot_controller/src/arduino/base_controller/src/main.cpp

/*
  main.cpp - DextroBot
  Omnidirectional robot powered by ROS and controlled via Arduino Mega.

  Main function that will constantly run on the Arduino Mega and will serve
  as ROS node for publishing sensors readings and for control the stepper motors
  that will act directly on the wheels of the robot based on the messages
  that are published on the ROS topic /cmd_vel
  Copyright (c) 2020 Antonio Brandi.  All right reserved.
*/

#include <Arduino.h>
#include <Dextrobot.h>
#include <ros.h>
#include <geometry_msgs/Vector3.h>
#include <std_msgs/String.h>

// Topic Names
// PUBLISH TOPIC
#define ROS_TOPIC_IMU "imu_raw"
#define ROS_TOPIC_RANGE_FRONT "range_front_raw"
#define ROS_TOPIC_RANGE_LEFT "range_left_raw"
#define ROS_TOPIC_RANGE_RIGHT "range_right_raw"
#define ROS_TOPIC_RANGE_BACK "range_back_raw"
// SUBSCRIBE TOPIC
#define ROS_TOPIC_CMD_VEL "cmd_vel"

// ROS message publish frequency
#define PUBLISH_DELAY 50 // 10Hz

// Init a ROS node on the Arduino controller
ros::NodeHandle nh;
// Publishers
std_msgs::String imu_msg;
std_msgs::String range_front_msg;
std_msgs::String range_left_msg;
std_msgs::String range_right_msg;
std_msgs::String range_back_msg;
ros::Publisher pub_range_front(ROS_TOPIC_RANGE_FRONT, &range_front_msg);
ros::Publisher pub_range_left(ROS_TOPIC_RANGE_LEFT, &range_left_msg);
ros::Publisher pub_range_right(ROS_TOPIC_RANGE_RIGHT, &range_right_msg);
ros::Publisher pub_range_back(ROS_TOPIC_RANGE_BACK, &range_back_msg);
ros::Publisher pub_imu(ROS_TOPIC_IMU, &imu_msg);

// Create an instance of the Robot with its methods
Dextrobot robot;

// Record the last time a publish operation happened
unsigned long publisher_timer;
int8_t publisher_turn = 0;

// Callback function that is called once a message is published on the topic /cmd_vel on which this Arduino is subscribed
void onCmdVelMsg(const geometry_msgs::Vector3& msg){
  // extract only useful parameters. No linear mouvement possible over z axis
  // and no rotation mouvements possible over x and y axis
  float x_lin = msg.x;
  float y_lin = msg.y;
  float z_ang = msg.z;

  // Move the robot according to the received velocity message
  if(x_lin>0){
    if(y_lin>0){
      // go forward right
      robot.goForwardRight(x_lin);
    } else if (y_lin<0){
      // go forward left
      robot.goForwardLeft(x_lin);
    } else{
      // go forward
      robot.goForward(x_lin);
    }
  }

  if(x_lin<0){
    if(y_lin>0){
      // go backward right
      robot.goBackwardRight(x_lin);
    } else if (y_lin<0){
      // go backward left
      robot.goBackwardLeft(x_lin);
    } else{
      // go backward
      robot.goBackward(x_lin);
    }
  }

  if(z_ang>0){
    // rotate clockwise
    robot.rotateClockwise(z_ang);
  } else if(z_ang<0){
    // rotate counterclockwise
    robot.rotateCounterClockwise(z_ang);
  }

  if(x_lin==0 && y_lin==0 && z_ang==0){
    // stop the robot
    robot.stop();
  }
}

// Subscribers
// CMD_VEL 
ros::Subscriber<geometry_msgs::Vector3> sub_cmd_vel(ROS_TOPIC_CMD_VEL, onCmdVelMsg );


void setup() {
  // cerate and initialize a ROS node on this Arduino controller
  nh.initNode();
  // Register the Subscribers
  nh.subscribe(sub_cmd_vel);
  // Register the Publishers
  nh.advertise(pub_range_front);
  nh.advertise(pub_range_left);
  nh.advertise(pub_range_right);
  nh.advertise(pub_range_back);
  nh.advertise(pub_imu);

  // Init the robot and it's stepper motor
  robot = Dextrobot();

  // Init the accelerometer
  while(!robot.imu.mpu.begin(MPU6050_SCALE_2000DPS, MPU6050_RANGE_2G))
  {
      delay(500);
  }
  // Calibrate gyroscope. The calibration must be at rest.
  // If you don't want calibrate, comment this line.
  robot.imu.mpu.calibrateGyro(); 
  // Set threshold sensivty. Default 3.
  // If you don't want use threshold, comment this line or set 0.
  robot.imu.mpu.setThreshold(1);

  publisher_timer = millis();
}

void loop() { 
  // move the stepper motor if needed
  robot.run();

  // read the actual status of the sensors
  robot.sense();

  if (millis() >= publisher_timer) {
    // compose and publish the sensor messages
    if(publisher_turn==0){
      String data_front_sonar = robot.sonar_1.composeStringMessage();
      int length = data_front_sonar.length();
      char data_final_front[length+1];
      data_front_sonar.toCharArray(data_final_front, length+1);
      range_front_msg.data = data_final_front;

      // publish the message
      pub_range_front.publish(&range_front_msg);

      publisher_turn++;
    }
    else if (publisher_turn==1){
      String data_left_sonar = robot.sonar_2.composeStringMessage();
      int length = data_left_sonar.length();
      char data_final_left[length+1];
      data_left_sonar.toCharArray(data_final_left, length+1);
      range_left_msg.data = data_final_left;

      // publish the message
      pub_range_left.publish(&range_left_msg);

      publisher_turn++;
    }
    else if (publisher_turn==2){
      String data_right_sonar = robot.sonar_3.composeStringMessage();
      int length = data_right_sonar.length();
      char data_final_right[length+1];
      data_right_sonar.toCharArray(data_final_right, length+1);
      range_right_msg.data = data_final_right;

      // publish the message
      pub_range_right.publish(&range_right_msg);

      publisher_turn++;
    }
    else{
      String data_back_sonar = robot.sonar_4.composeStringMessage();
      int length = data_back_sonar.length();
      char data_final_back[length+1];
      data_back_sonar.toCharArray(data_final_back, length+1);
      range_back_msg.data = data_final_back;

      // publish the message
      pub_range_back.publish(&range_back_msg);

      publisher_turn = 0;
    }   

    String data = robot.imu.composeStringMessage();
    int length = data.length();
    char data_final[length+1];
    data.toCharArray(data_final, length+1);
    imu_msg.data = data_final;

    // publish the messages
    pub_imu.publish(&imu_msg);    

    // update the last time a message has been published via ROS
    publisher_timer = millis() + PUBLISH_DELAY;
  }

  // Keep ROS Node Up & Running
  nh.spinOnce();
}
