AntoBrandi/Dextro-Bot/ROS/dextrobot_ws/src/dextrobot_controller/src/arduino/base_controller/src/Dextrobot.h

/*
  Dextrobot.h - DextroBot
  Class that cointains the implementation of the low level omnidirectional mouvements
  for the robot based on the willing direction of the mouvement the stepper motors are controlled
  differently and independently in order to achieve the desired mouvement.
  Copyright (c) 2020 Antonio Brandi.  All right reserved.
*/
#include <Stepper.h>
#include <Imu.h>
#include <Sonar.h>

// Arduino PINS 
// CNC Shield
#define ENABLE_SHIELD 8
// MOTOR 1 - Front Left
#define DIR_STEPPER_1 5
#define STEP_STEPPER_1 2
// MOTOR 2 - Front Right
#define DIR_STEPPER_2 6
#define STEP_STEPPER_2 3
// MOTOR 3 - Back Left
#define DIR_STEPPER_3 7
#define STEP_STEPPER_3 4
// MOTOR 4 - Back Right
#define DIR_STEPPER_4 13
#define STEP_STEPPER_4 12
// SONAR 1 - Front sonar
#define TRIGGER_FRONT_SONAR 22
#define ECHO_FRONT_SONAR 23
// SONAR 2 - Left sonar
#define TRIGGER_LEFT_SONAR 26
#define ECHO_LEFT_SONAR 27
// SONAR 3 - Right sonar
#define TRIGGER_RIGHT_SONAR 24
#define ECHO_RIGHT_SONAR 25
// SONAR 4 - Back sonar
#define TRIGGER_BACK_SONAR 28
#define ECHO_BACK_SONAR 29

#ifndef Dextrobot_h
#define Dextrobot_h

class Dextrobot
{
private:
    // Motors
    Stepper motor_1 = Stepper(STEP_STEPPER_1, DIR_STEPPER_1);
    Stepper motor_2 = Stepper(STEP_STEPPER_2, DIR_STEPPER_2);
    Stepper motor_3 = Stepper(STEP_STEPPER_3, DIR_STEPPER_3);
    Stepper motor_4 = Stepper(STEP_STEPPER_4, DIR_STEPPER_4);    

public:
    // Attributes
    Imu imu = Imu();
    Sonar sonar_1 = Sonar(TRIGGER_FRONT_SONAR, ECHO_FRONT_SONAR);
    Sonar sonar_2 = Sonar(TRIGGER_LEFT_SONAR, ECHO_LEFT_SONAR);
    Sonar sonar_3 = Sonar(TRIGGER_RIGHT_SONAR, ECHO_RIGHT_SONAR);
    Sonar sonar_4 = Sonar(TRIGGER_BACK_SONAR, ECHO_BACK_SONAR);

    // Functions
    Dextrobot(/* args */);
    ~Dextrobot();

    // omnidirectional mouvement functions
    void goForward(float velocity);
    void goBackward(float velocity);
    void goRight(float velocity);
    void goLeft(float velocity);
    void goForwardRight(float velocity);
    void goForwardLeft(float velocity);
    void goBackwardRight(float velocity);
    void goBackwardLeft(float velocity);
    void rotateClockwise(float velocity);
    void rotateCounterClockwise(float velocity);
    void stop();

    // sensor functions
    void sense();
    void run();
};


#endif
