AntoBrandi/Dextro-Bot/ROS/dextrobot_ws/src/dextrobot_controller/src/arduino/base_controller/src/Imu.h

#include <Wire.h>
#include <MPU6050.h>
#include <time.h>

#ifndef Imu_h
#define Imu_h

class Imu
{
    private:
        static const int MPU_addr = 0x68;  // I2C address of the MPU-6050
        // linear acceleration
        float AcX = 0;
        float AcY = 0;
        float AcZ = 0;
        // orientation
        int pitch = 0;
        int roll = 0;
        float yaw = 0;
        float toRadians(float degree);
        // time mangement
        unsigned long lastRead;
    public:
        MPU6050 mpu;
        Imu(/* args */);
        ~Imu();
        void sense();
        String composeStringMessage();
};


#endif
